rowr111/blinky-badge-light/blinky-badge-light/main/led_control.h

#ifndef LED_CONTROL_H
#define LED_CONTROL_H

#include <stdint.h>
#include <stdbool.h>
#include "genes.h"

void init_leds(void);
void set_pattern(int pattern_id);
void set_brightness(int index);
void update_leds(uint8_t *framebuffer);
uint8_t calculate_pattern_hue(const genome *g, int led_index, int loop);
void render_pattern(int index, uint8_t *framebuffer, int loop);
void lighting_task(void *param);

void flash_feedback_pattern(void);
void safety_pattern(uint8_t *framebuffer);

extern volatile bool flash_active; 
extern uint8_t effective_brightness;


// Constants
#define MAX_BRIGHTNESS 255      // Maximum brightness level
#define NUM_PATTERNS 5          // Number of lighting patterns
#define NUM_BRIGHTNESS_LEVELS 5 // Number of brightness levels

#endif // LED_CONTROL_H
