rowr111/blinky-badge-light/blinky-badge-light/main/genes.h

#ifndef GENES_H
#define GENES_H

#include <stdint.h>
#include <string.h>

typedef struct {
    uint8_t cd_period;       // Controls period of sine wave (e.g., pattern speed)
    uint8_t cd_rate;         // Amplitude or "volume" of brightness modulation
    uint8_t cd_dir;          // Direction for certain effects
    uint8_t sat;             // Saturation level
    uint8_t hue_base;        // Base hue
    uint8_t hue_rate;        // Hue change rate
    uint8_t hue_dir;         // Direction of hue change
    uint8_t hue_bound;       // Maximum hue
    uint8_t lin;             // Linear brightness modifier
    uint8_t nonlin;          // Nonlinearity (gamma correction or other tweaks)
} genome;

void generate_gene(genome *g);

#endif // GENES_H
