rowr111/blinky-badge-light/blinky-badge-light/main/microphone.h

#ifndef MICROPHONE_H
#define MICROPHONE_H

#include <stdint.h>

extern volatile float current_dB_level;
extern volatile float dB_brightness_level;
extern volatile float smooth_dB_brightness_level;

void init_microphone(void);
float get_sound_level(void); // Returns decibel level
void microphone_task(void *param);
void i2s_matrix_dump_task(void *param);

#endif // MICROPHONE_H
